jwxxjq/air_inspector/host_pc_script/fig3.png

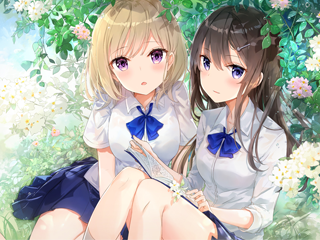
host_pc_script/fig3.png
