jwxxjq/air_inspector/host_pc_script/fig6.png

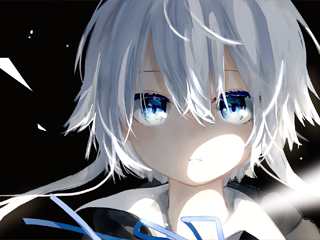
host_pc_script/fig6.png
