jwxxjq/air_inspector/host_pc_script/fig9.png

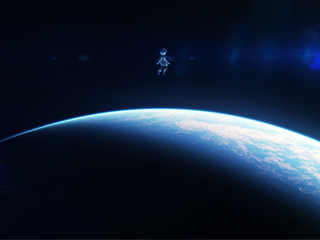
host_pc_script/fig9.png
